tymancjo/fourleg/Python/img/aronmk2.jpg

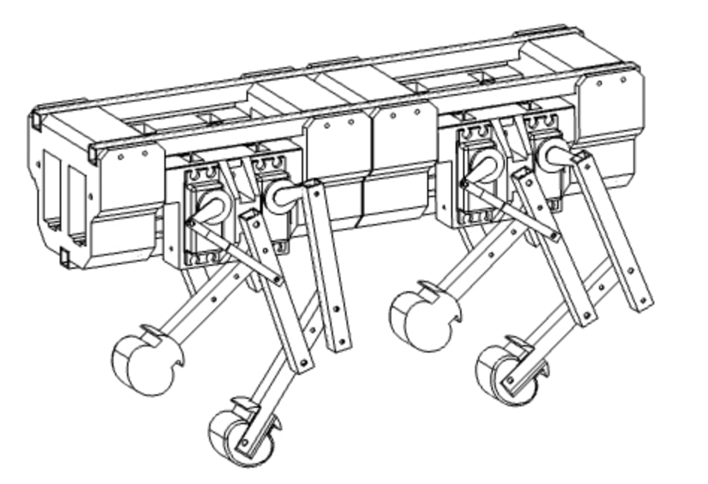
Python/img/aronmk2.jpg
